djordjevujic/slat-sort-cam-dark-box/downloads/2020-extrusions-fittings-1.snapshot.27/Set.png

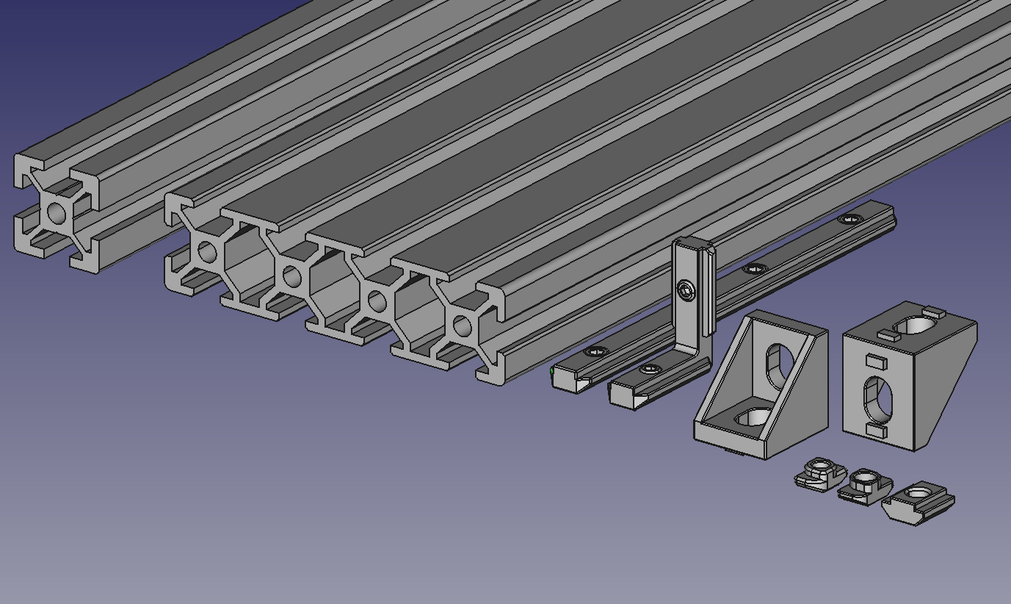
downloads/2020-extrusions-fittings-1.snapshot.27/Set.png
