djordjevujic/slat-sort-cam-dark-box/downloads/t-nut-m5-for-2020-profile-1.snapshot.5/T-Nut 2020 5mm.jpeg

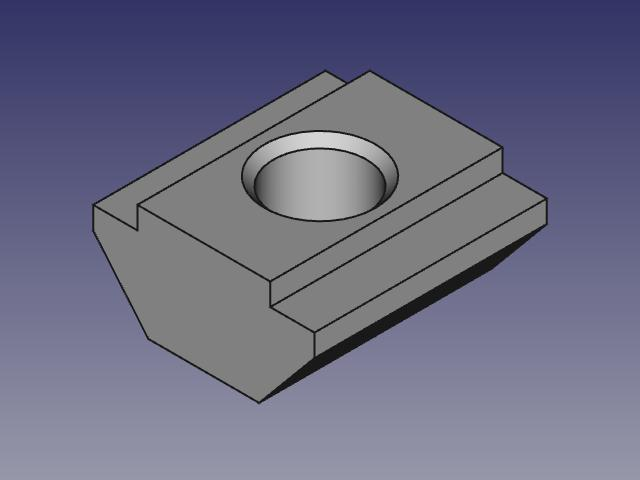
downloads/t-nut-m5-for-2020-profile-1.snapshot.5/T-Nut 2020 5mm.jpeg
