djordjevujic/slat-sort-cam-dark-box/parts/cam_holder/cam_holder_plate.FCStd

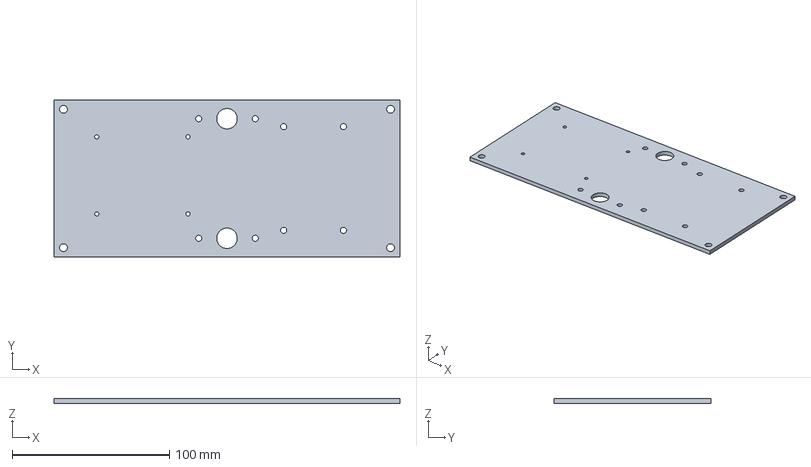
[picture p18: CAD file, 2025-01-29]
parts/cam_holder/cam_holder_plate.FCStd
220.0 x 100.0 x 3.00 mm
