djordjevujic/slat-sort-cam-dark-box/parts/T-Slot_20_height.FCStd

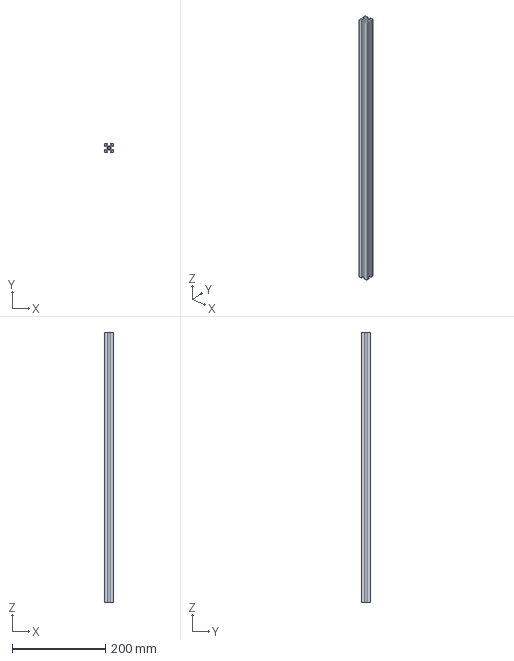
[picture p19: CAD file, 2025-01-21]
parts/T-Slot_20_height.FCStd
20.0 x 20.0 x 580.0 mm
