djordjevujic/slat-sort-cam-dark-box/secondary/nuts_hexagonal.FCStd

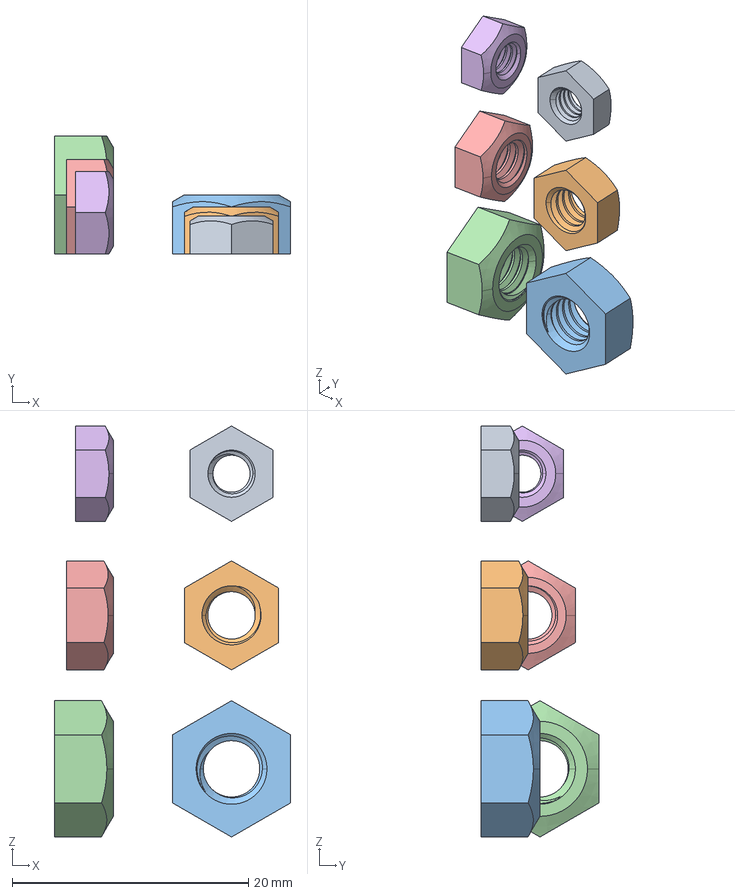
[picture p20: CAD file, 2025-01-15]
secondary/nuts_hexagonal.FCStd
20.0 x 10.0 x 34.8 mm
Hexagonal Nut M4_CBALN4
Hexagonal Nut M5_CBALN5
Hexagonal Nut M6_CBALN6
Hexagonal Nut M6_CBALN007
Hexagonal Nut M5_CBALN006
Hexagonal Nut M4_CBALN005
