djordjevujic/slat-sort-cam-dark-box/downloads/2020-extrusions-fittings-1.snapshot.27/2040 Extrusion.step

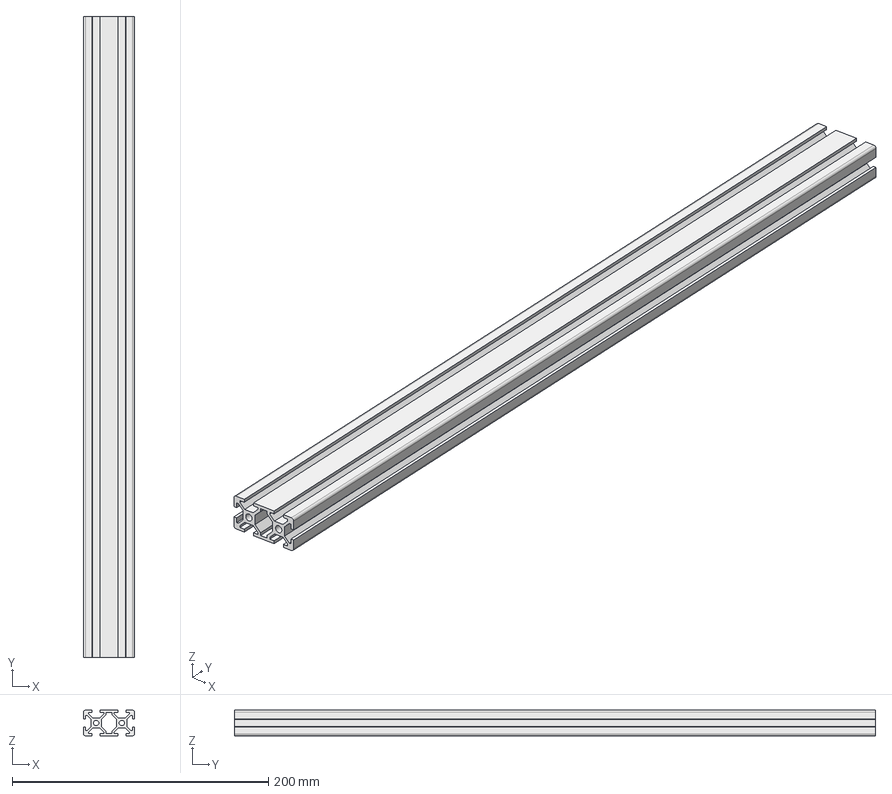
[picture p21: CAD file, 2025-01-11]
downloads/2020-extrusions-fittings-1.snapshot.27/2040 Extrusion.step
40.0 x 500.0 x 20.0 mm
