djordjevujic/slat-sort-cam-dark-box/downloads/raspberry-pi5-machine-vision-camera-case-1.snapshot.10/Raspberry Pi HQ Camera.step

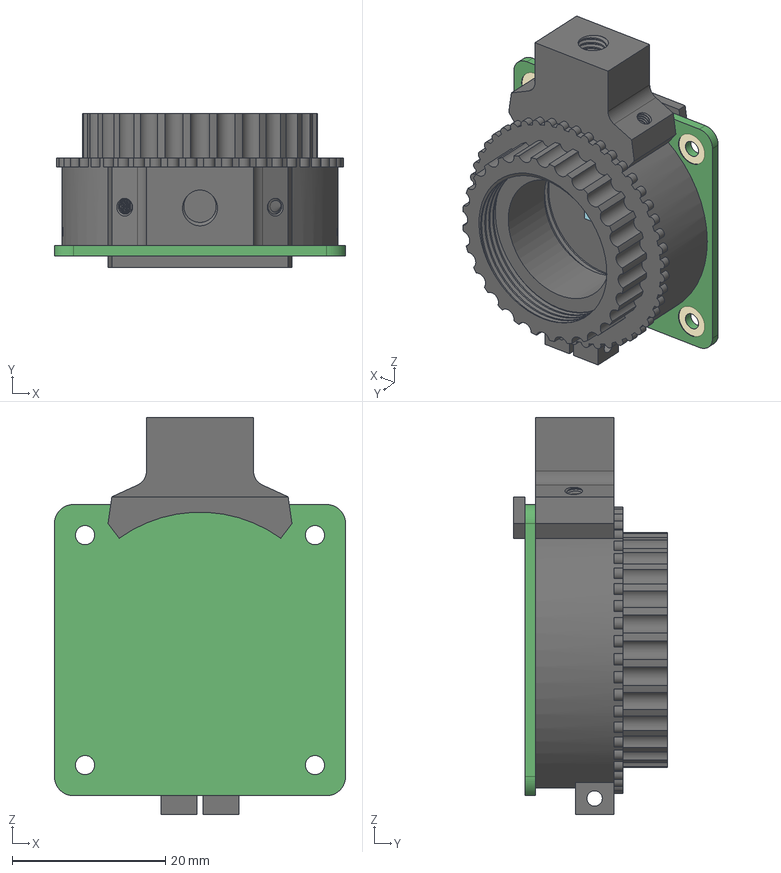
[picture p22: CAD file, 2025-01-11]
downloads/raspberry-pi5-machine-vision-camera-case-1.snapshot.10/Raspberry Pi HQ Camera.step
38.0 x 20.1 x 51.8 mm
