djordjevujic/slat-sort-cam-dark-box/downloads/raspberry_pi_4_model_b.FCStd

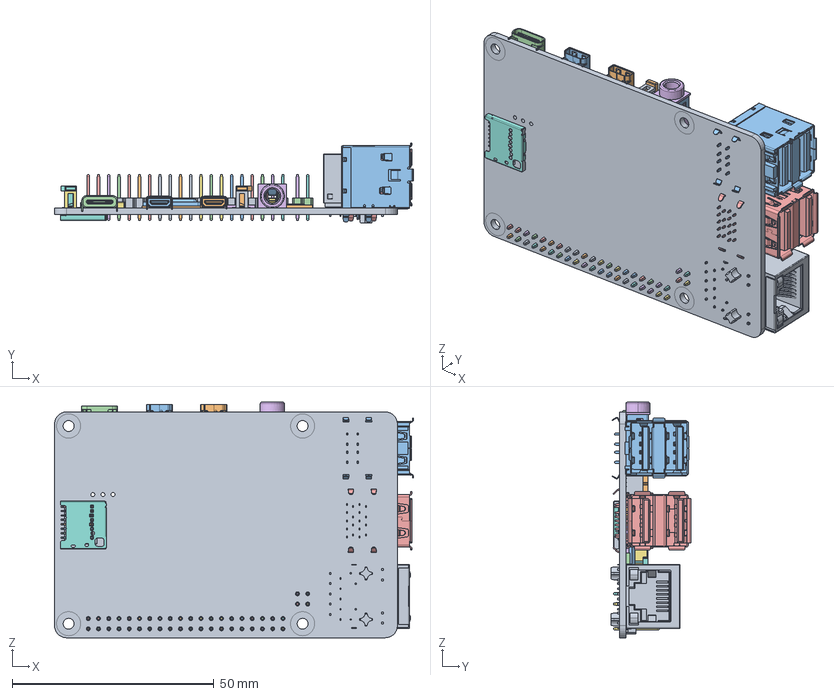
[picture p23: CAD file, 2025-01-11]
downloads/raspberry_pi_4_model_b.FCStd
89.0 x 19.9 x 58.4 mm
PCB, RPi4ModelB
Broadcom BCM2711B0 CPU, RPi4ModelB
Broadcom BCM2711B0 CPU, RPi4ModelB001
2.54 mm DUPONT MALE PIN HEADER, POE, 2X2, RPi4ModelB
2.54 mm DUPONT MALE PIN HEADER, POE, 2X2, RPi4ModelB001
2.54 mm DUPONT MALE PIN HEADER, POE, 2X2, RPi4ModelB002
2.54 mm DUPONT MALE PIN HEADER, POE, 2X2, RPi4ModelB003
2.54 mm DUPONT MALE PIN HEADER, POE, 2X2, RPi4ModelB004
2.54 mm DUPONT MALE PIN HEADER, IO, 2X20, RPi4ModelB
2.54 mm DUPONT MALE PIN HEADER, IO, 2X20, RPi4ModelB001
2.54 mm DUPONT MALE PIN HEADER, IO, 2X20, RPi4ModelB002
2.54 mm DUPONT MALE PIN HEADER, IO, 2X20, RPi4ModelB003
2.54 mm DUPONT MALE PIN HEADER, IO, 2X20, RPi4ModelB004
2.54 mm DUPONT MALE PIN HEADER, IO, 2X20, RPi4ModelB005
2.54 mm DUPONT MALE PIN HEADER, IO, 2X20, RPi4ModelB006
2.54 mm DUPONT MALE PIN HEADER, IO, 2X20, RPi4ModelB007
2.54 mm DUPONT MALE PIN HEADER, IO, 2X20, RPi4ModelB008
2.54 mm DUPONT MALE PIN HEADER, IO, 2X20, RPi4ModelB009
2.54 mm DUPONT MALE PIN HEADER, IO, 2X20, RPi4ModelB010
2.54 mm DUPONT MALE PIN HEADER, IO, 2X20, RPi4ModelB011
2.54 mm DUPONT MALE PIN HEADER, IO, 2X20, RPi4ModelB012
2.54 mm DUPONT MALE PIN HEADER, IO, 2X20, RPi4ModelB013
2.54 mm DUPONT MALE PIN HEADER, IO, 2X20, RPi4ModelB014
2.54 mm DUPONT MALE PIN HEADER, IO, 2X20, RPi4ModelB015
2.54 mm DUPONT MALE PIN HEADER, IO, 2X20, RPi4ModelB016
2.54 mm DUPONT MALE PIN HEADER, IO, 2X20, RPi4ModelB017
2.54 mm DUPONT MALE PIN HEADER, IO, 2X20, RPi4ModelB018
2.54 mm DUPONT MALE PIN HEADER, IO, 2X20, RPi4ModelB019
2.54 mm DUPONT MALE PIN HEADER, IO, 2X20, RPi4ModelB020
2.54 mm DUPONT MALE PIN HEADER, IO, 2X20, RPi4ModelB021
2.54 mm DUPONT MALE PIN HEADER, IO, 2X20, RPi4ModelB022
2.54 mm DUPONT MALE PIN HEADER, IO, 2X20, RPi4ModelB023
2.54 mm DUPONT MALE PIN HEADER, IO, 2X20, RPi4ModelB024
2.54 mm DUPONT MALE PIN HEADER, IO, 2X20, RPi4ModelB025
2.54 mm DUPONT MALE PIN HEADER, IO, 2X20, RPi4ModelB026
2.54 mm DUPONT MALE PIN HEADER, IO, 2X20, RPi4ModelB027
2.54 mm DUPONT MALE PIN HEADER, IO, 2X20, RPi4ModelB028
2.54 mm DUPONT MALE PIN HEADER, IO, 2X20, RPi4ModelB029
2.54 mm DUPONT MALE PIN HEADER, IO, 2X20, RPi4ModelB030
2.54 mm DUPONT MALE PIN HEADER, IO, 2X20, RPi4ModelB031
2.54 mm DUPONT MALE PIN HEADER, IO, 2X20, RPi4ModelB032
2.54 mm DUPONT MALE PIN HEADER, IO, 2X20, RPi4ModelB033
2.54 mm DUPONT MALE PIN HEADER, IO, 2X20, RPi4ModelB034
2.54 mm DUPONT MALE PIN HEADER, IO, 2X20, RPi4ModelB035
2.54 mm DUPONT MALE PIN HEADER, IO, 2X20, RPi4ModelB036
2.54 mm DUPONT MALE PIN HEADER, IO, 2X20, RPi4ModelB037
2.54 mm DUPONT MALE PIN HEADER, IO, 2X20, RPi4ModelB038
2.54 mm DUPONT MALE PIN HEADER, IO, 2X20, RPi4ModelB039
2.54 mm DUPONT MALE PIN HEADER, IO, 2X20, RPi4ModelB040
Camera Connector, RPi4ModelB
Camera Connector, RPi4ModelB001
Camera Connector, RPi4ModelB002
Camera Connector, RPi4ModelB003
Camera Connector, RPi4ModelB004
Camera Connector, RPi4ModelB005
Camera Connector, RPi4ModelB006
Camera Connector, RPi4ModelB007
Camera Connector, RPi4ModelB008
Camera Connector, RPi4ModelB009
Camera Connector, RPi4ModelB010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
