djordjevujic/slat-sort-cam-dark-box/exported_step/plate_roof-plate_roof.step

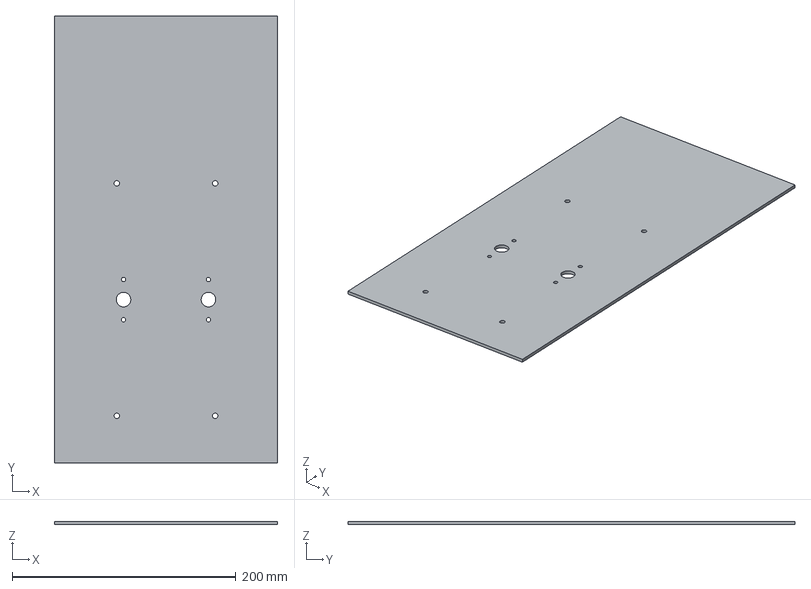
[picture p24: CAD file, 2025-01-22]
exported_step/plate_roof-plate_roof.step
200.0 x 400.0 x 3.00 mm
