djordjevujic/slat-sort-cam-dark-box/parts/cam_holder/cam_holder_connector.FCStd

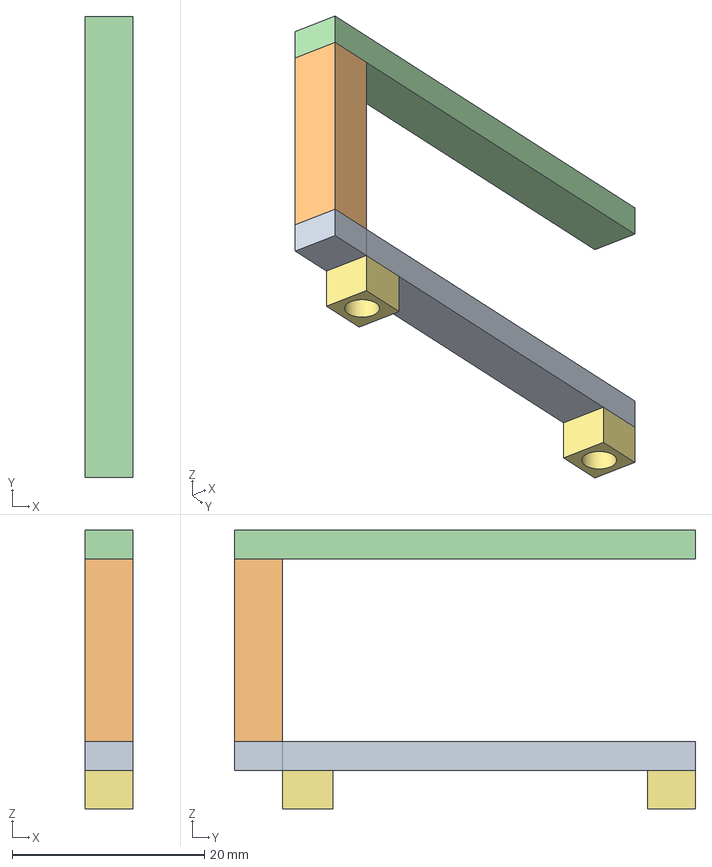
[picture p25: CAD file, 2025-01-11]
parts/cam_holder/cam_holder_connector.FCStd
5.00 x 48.0 x 29.0 mm
