djordjevujic/slat-sort-cam-dark-box/parts/T-Slot_20_length.FCStd

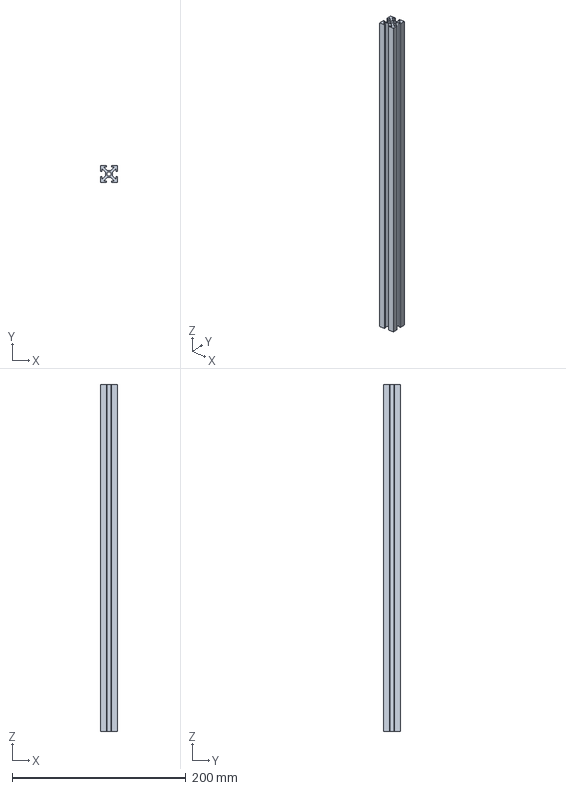
[picture p26: CAD file, 2025-01-21]
parts/T-Slot_20_length.FCStd
20.0 x 20.0 x 400.0 mm
