djordjevujic/slat-sort-cam-dark-box/downloads/20mm Aluminium T-Slot Extrusion Profile.FCStd

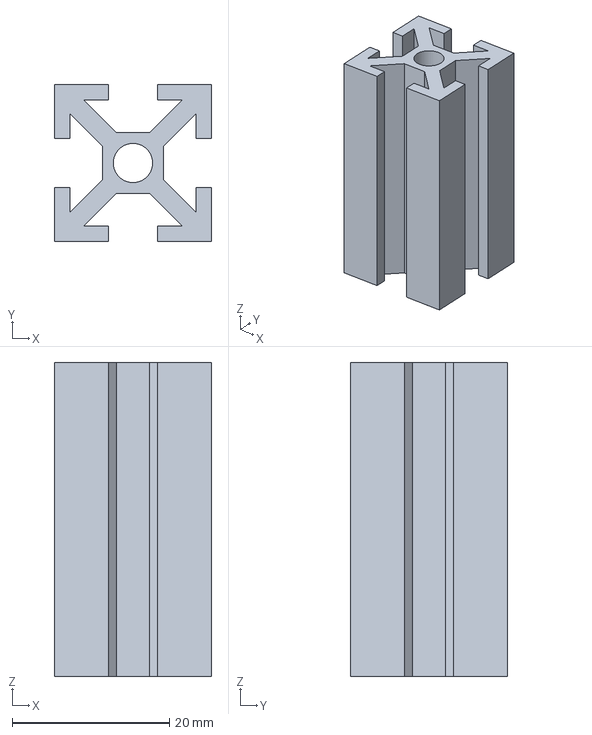
[picture p28: CAD file, 2025-01-11]
downloads/20mm Aluminium T-Slot Extrusion Profile.FCStd
20.0 x 20.0 x 40.0 mm
