djordjevujic/slat-sort-cam-dark-box/downloads/raspberry-pi5-machine-vision-camera-case-1.snapshot.10/RPI-001 RPICAM ENCLOSURE.STEP

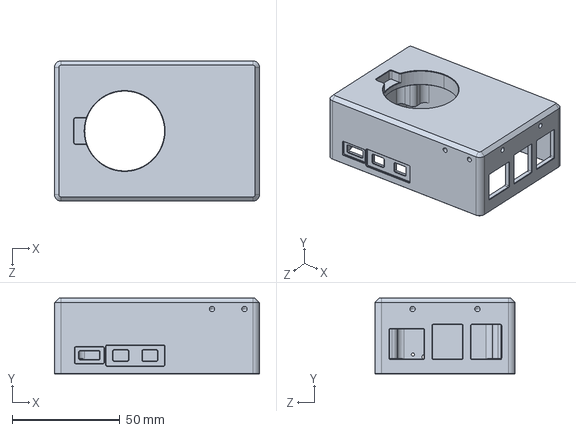
[picture p29: CAD file, 2025-01-11]
downloads/raspberry-pi5-machine-vision-camera-case-1.snapshot.10/RPI-001 RPICAM ENCLOSURE.STEP
95.0 x 35.0 x 65.0 mm
