djordjevujic/slat-sort-cam-dark-box/exported_step/plate_side-plate_side.step

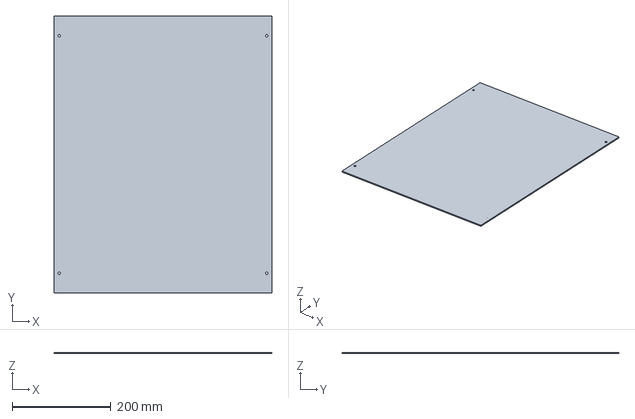
[picture p30: CAD file, 2025-01-22]
exported_step/plate_side-plate_side.step
440.0 x 560.0 x 3.00 mm
