djordjevujic/slat-sort-cam-dark-box/parts/cam_holder/cam_holder_base-cam_holder_base.stl

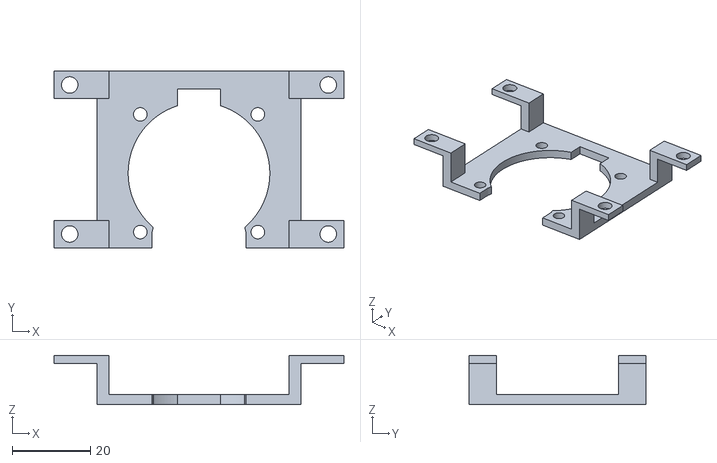
[picture p31: CAD file, 2025-01-11]
parts/cam_holder/cam_holder_base-cam_holder_base.stl
73.9 x 45.0 x 12.5
