djordjevujic/slat-sort-cam-dark-box/parts/T-Slot_20_width.FCStd

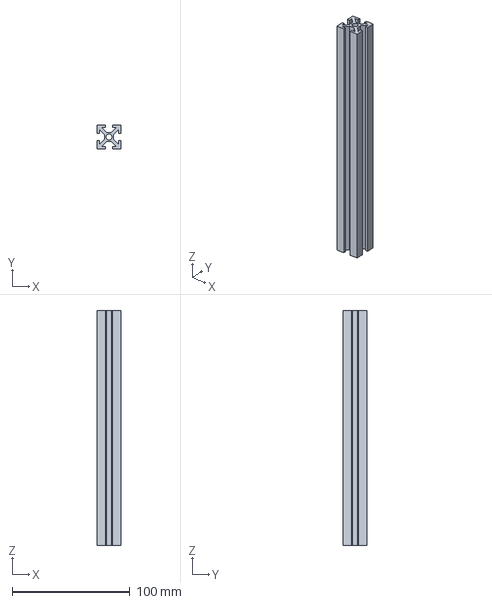
[picture p32: CAD file, 2025-01-21]
parts/T-Slot_20_width.FCStd
20.0 x 20.0 x 200.0 mm
