djordjevujic/slat-sort-cam-dark-box/downloads/2020-extrusions-fittings-1.snapshot.27/FreeCAD Files/Set.FCStd

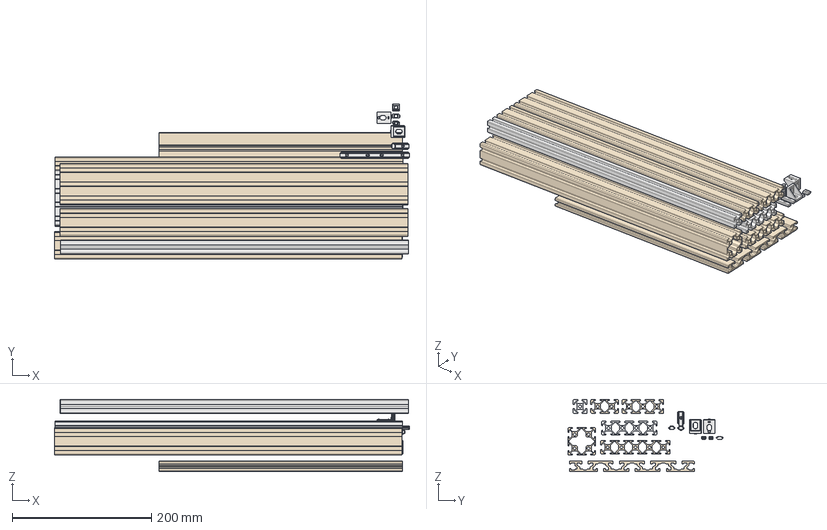
[picture p34: CAD file, 2025-01-11]
downloads/2020-extrusions-fittings-1.snapshot.27/FreeCAD Files/Set.FCStd
510.6 x 223.3 x 103.7 mm
2020 Corner Bracket_001
2020 Corner Bracket_002
2020 Extrusion Inside Corner Bracket_001
M4 T-Nut_001
M5 T-Nut_001
M5 Block T-Nut_001
2020 Extrusion_001
2080 Extrusion Detailed_001
2020 Extrusion Straight Internal Connector_001
2040 Extrusion_001
20100 Extrusion Detailed_001
4040 Extrusion_001
2060 Extrusion-Body1_001
300x180x15mm T-Slot Profile Aluminum-Cut003_001
