djordjevujic/slat-sort-cam-dark-box/secondary/linear_slide.FCStd

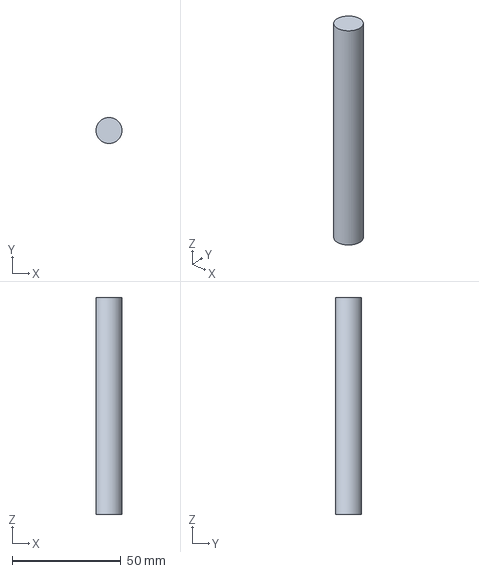
[picture p35: CAD file, 2025-01-11]
secondary/linear_slide.FCStd
12.0 x 12.0 x 100.0 mm
