djordjevujic/slat-sort-cam-dark-box/downloads/2020-extrusions-fittings-1.snapshot.27/FreeCAD Files/2020 Extrusion.FCStd

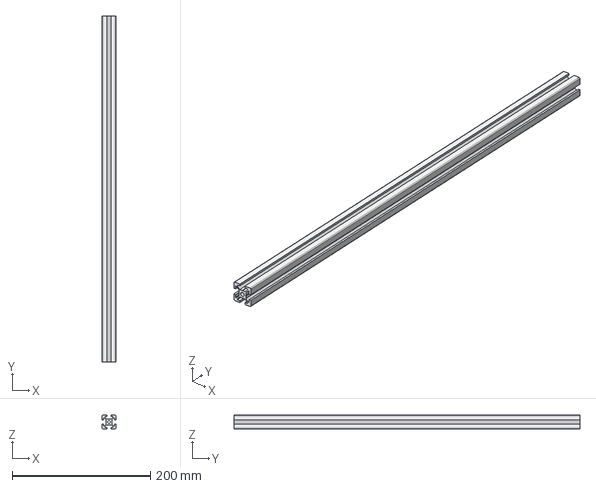
[picture p36: CAD file, 2025-01-11]
downloads/2020-extrusions-fittings-1.snapshot.27/FreeCAD Files/2020 Extrusion.FCStd
20.0 x 500.0 x 20.0 mm
