djordjevujic/slat-sort-cam-dark-box/parts/roof_holder.FCStd

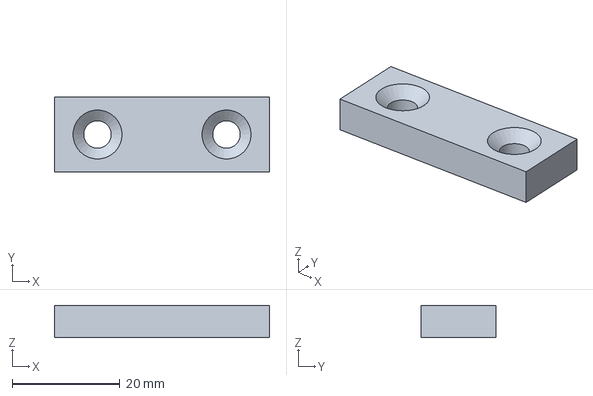
[picture p37: CAD file, 2025-01-20]
parts/roof_holder.FCStd
40.0 x 14.0 x 6.00 mm
