djordjevujic/slat-sort-cam-dark-box/parts/plate_holder.FCStd

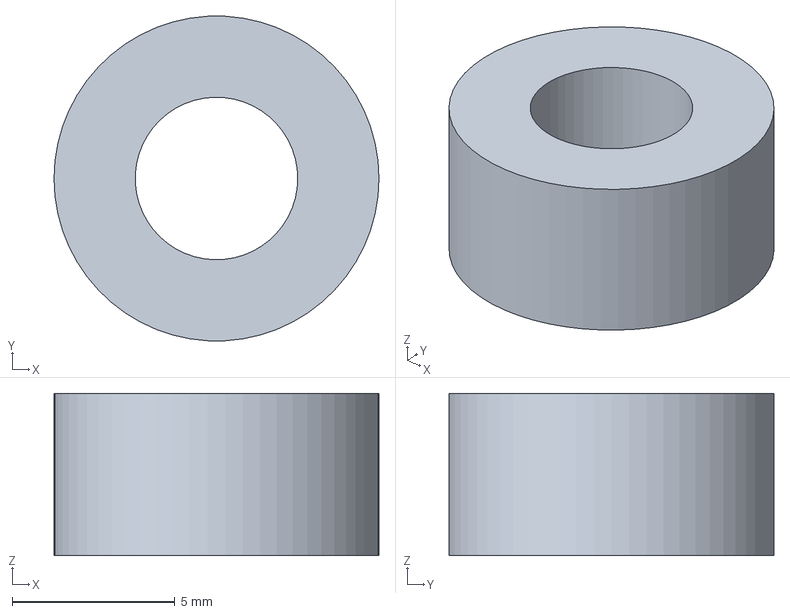
[picture p38: CAD file, 2025-01-11]
parts/plate_holder.FCStd
10.0 x 9.99 x 5.00 mm
