djordjevujic/slat-sort-cam-dark-box/downloads/2020-extrusions-fittings-1.snapshot.27/2020 Extrusion Straight Internal Connector.step

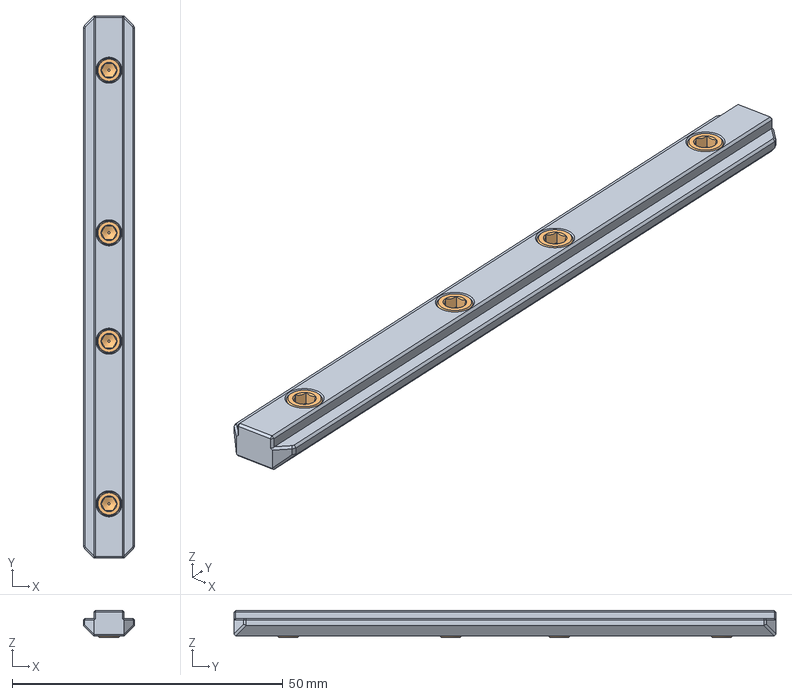
[picture p39: CAD file, 2025-01-11]
downloads/2020-extrusions-fittings-1.snapshot.27/2020 Extrusion Straight Internal Connector.step
9.50 x 100.0 x 5.00 mm
M5x5-Screw
M5x5-Screw004
M5x5-Screw005
M5x5-Screw006
