djordjevujic/slat-sort-cam-dark-box/downloads/2020-extrusions-fittings-1.snapshot.27/2020 Extrusion Inside Corner Bracket.step

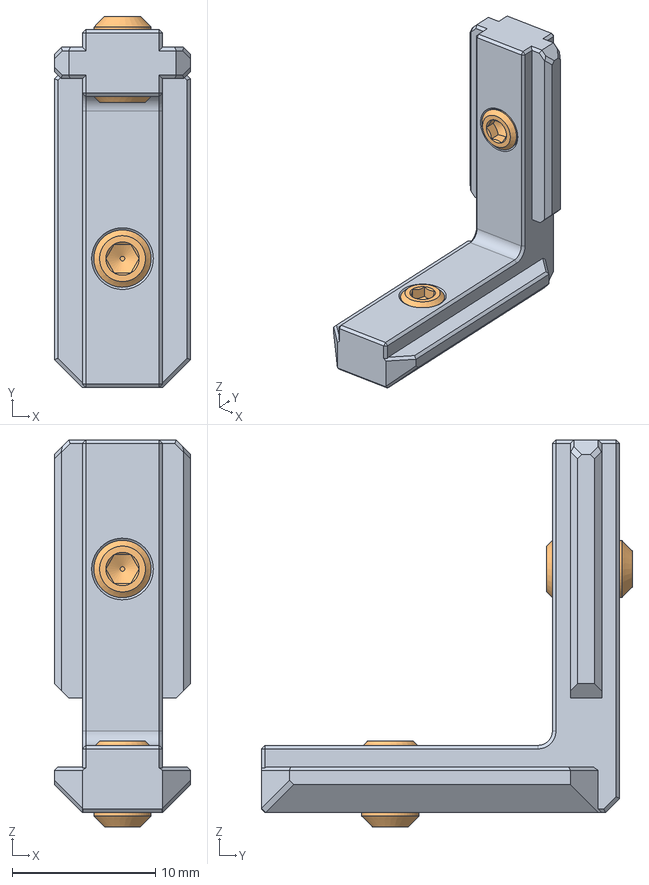
[picture p40: CAD file, 2025-01-11]
downloads/2020-extrusions-fittings-1.snapshot.27/2020 Extrusion Inside Corner Bracket.step
9.50 x 25.9 x 27.0 mm
M4x6-Screw
M4x6-Screw001
