djordjevujic/slat-sort-cam-dark-box/downloads/2020-extrusions-fittings-1.snapshot.27/300x180x15mm T-Slot Profile Aluminum.step

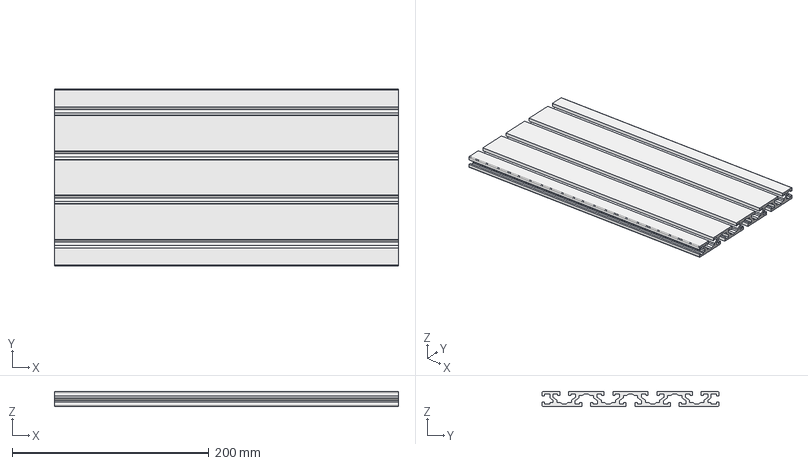
[picture p41: CAD file, 2025-01-11]
downloads/2020-extrusions-fittings-1.snapshot.27/300x180x15mm T-Slot Profile Aluminum.step
350.0 x 180.0 x 15.0 mm
