djordjevujic/slat-sort-cam-dark-box/downloads/2020-extrusions-fittings-1.snapshot.27/4040 Extrusion.step

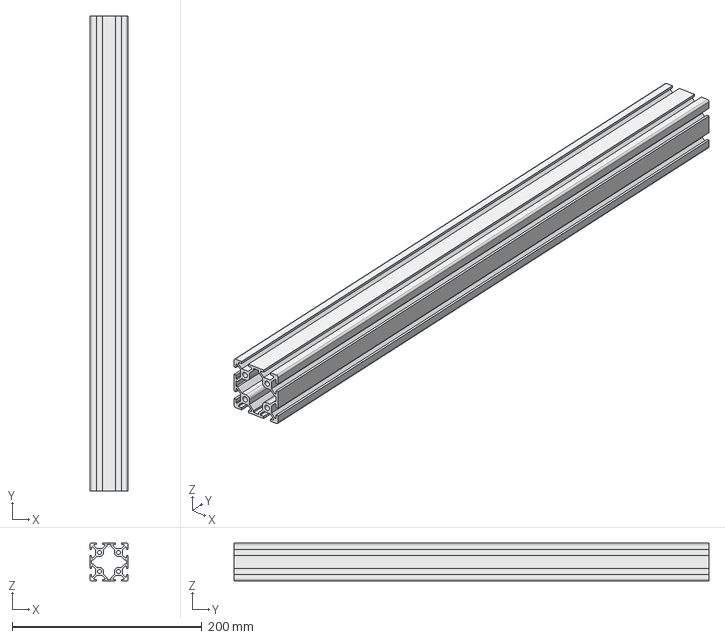
[picture p42: CAD file, 2025-01-11]
downloads/2020-extrusions-fittings-1.snapshot.27/4040 Extrusion.step
40.0 x 500.0 x 40.0 mm
